wyunreal/jukebox/hardware/3d-models/Electronic support/FuseCase.FCStd

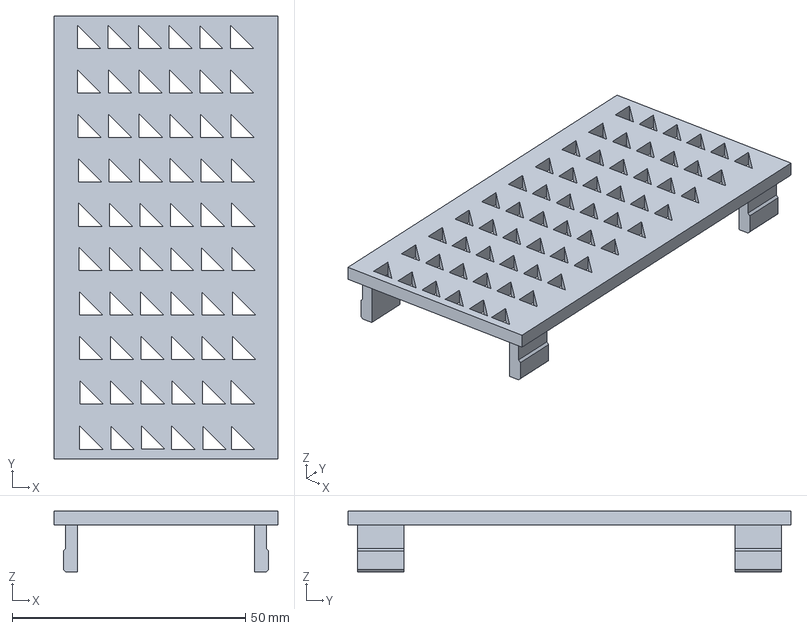
[picture p15: CAD file, 2026-09-22]
hardware/3d-models/Electronic support/FuseCase.FCStd
48.0 x 95.0 x 13.0 mm
