wyunreal/jukebox/hardware/3d-models/hdd/HddSupportWall.FCStd

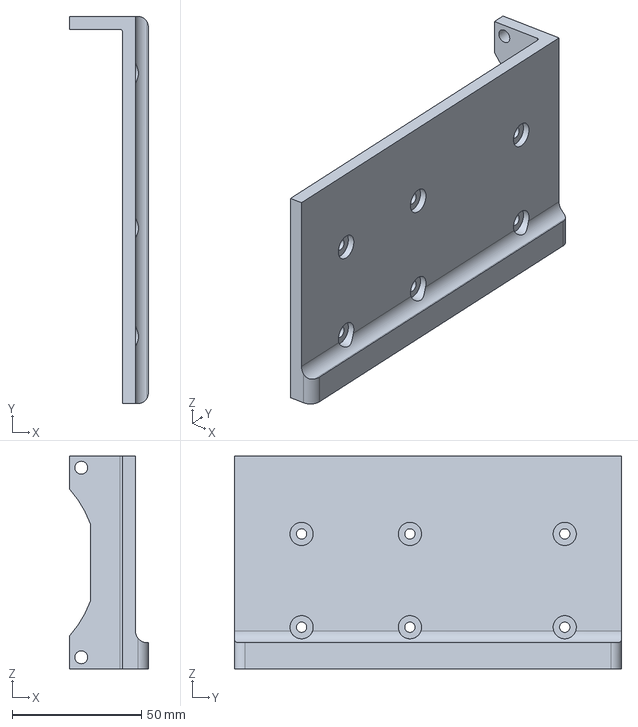
[picture p16: CAD file, 2026-09-22]
hardware/3d-models/hdd/HddSupportWall.FCStd
30.5 x 150.0 x 82.5 mm
