wyunreal/jukebox/hardware/3d-models/Pi support/PiSupport.FCStd

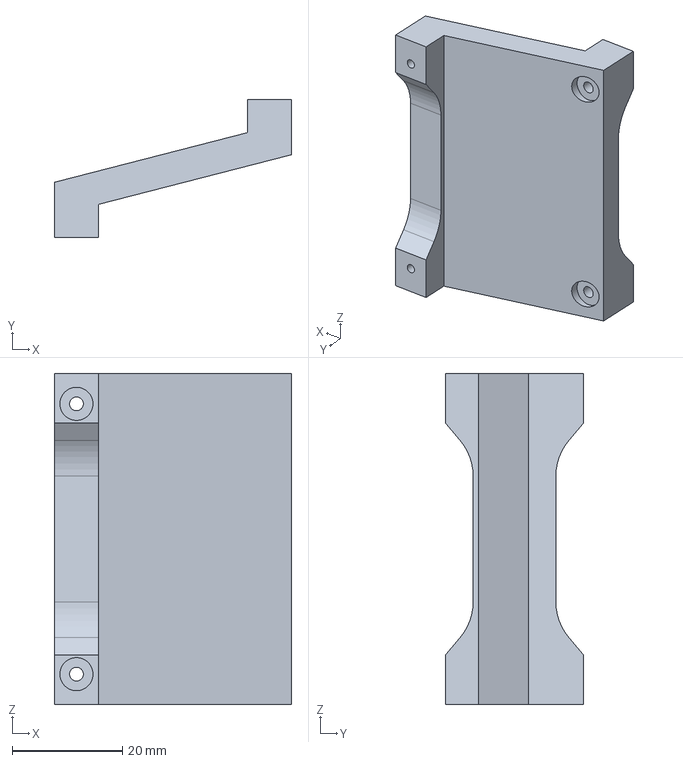
[picture p17: CAD file, 2026-09-22]
hardware/3d-models/Pi support/PiSupport.FCStd
43.0 x 25.0 x 60.0 mm
