wyunreal/jukebox/hardware/3d-models/screen/screenSupportBottomRight.FCStd

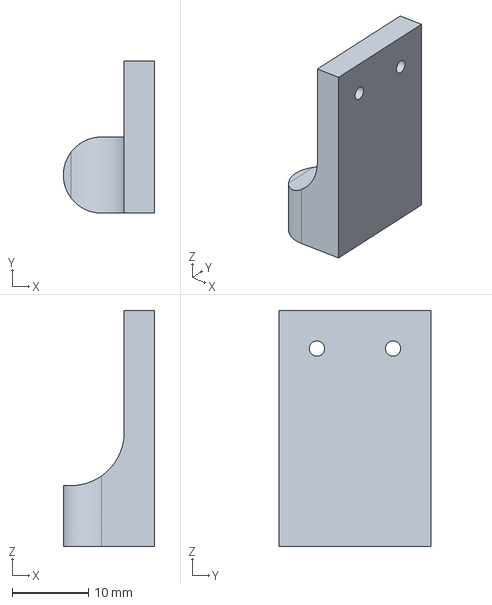
[picture p18: CAD file, 2026-09-22]
hardware/3d-models/screen/screenSupportBottomRight.FCStd
12.0 x 20.0 x 31.0 mm
