wyunreal/jukebox/hardware/3d-models/screen/screenJoint.FCStd

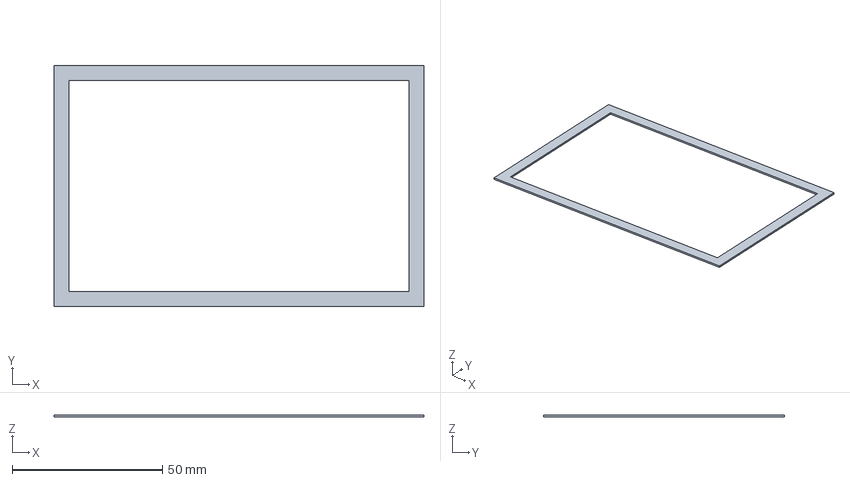
[picture p19: CAD file, 2026-09-22]
hardware/3d-models/screen/screenJoint.FCStd
123.0 x 80.0 x 0.75 mm
