wyunreal/jukebox/hardware/3d-models/screen/screenSupportTopRight.FCStd

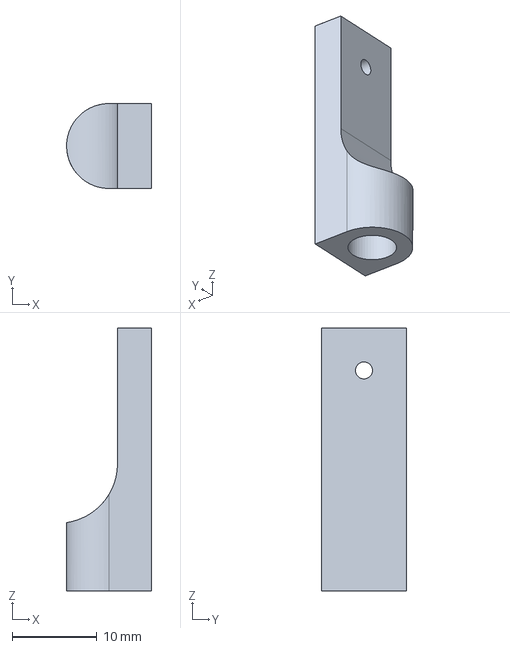
[picture p20: CAD file, 2026-09-22]
hardware/3d-models/screen/screenSupportTopRight.FCStd
10.0 x 10.0 x 31.0 mm
